BlockchainCommons/lethekit/doc/images/lethekit-1280x640.jpg

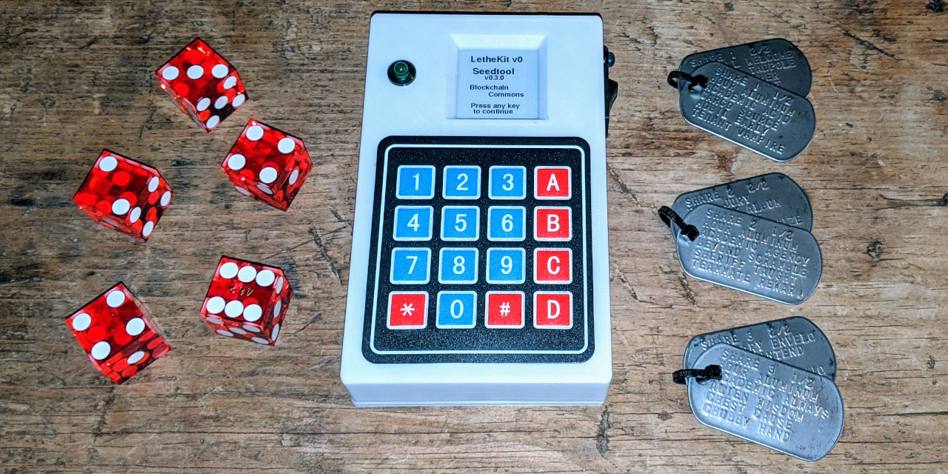
doc/images/lethekit-1280x640.jpg
