BlockchainCommons/lethekit/images/lk-xpub+prv-ex.jpg

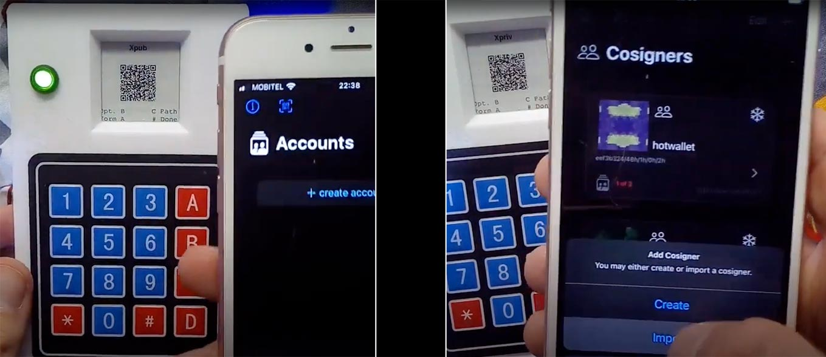
images/lk-xpub+prv-ex.jpg
