BlockchainCommons/lethekit/lethekit.jpg

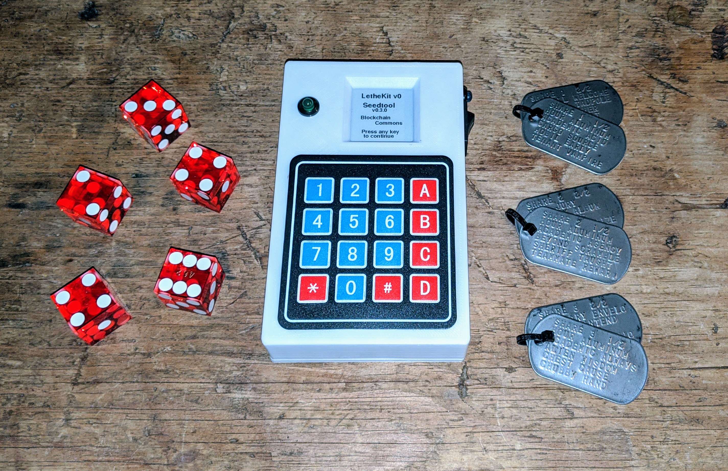
lethekit.jpg
