BlockchainCommons/lethekit/seedtool/doc/images/wallet.png

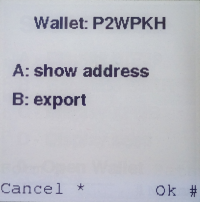
seedtool/doc/images/wallet.png
