BlockchainCommons/lethekit/deps/bc-ur-arduino/src/fountain-encoder.hpp

//
//  fountain-encoder.hpp
//
//  Copyright © 2020 by Blockchain Commons, LLC
//  Licensed under the "BSD-2-Clause Plus Patent License"
//

#ifndef BC_UR_FOUNTAIN_ENCODER_HPP
#define BC_UR_FOUNTAIN_ENCODER_HPP

#include <stddef.h>
#include <vector>
#include <exception>
#include "utils.hpp"
//#include "util.h"
#include "fountain-utils.hpp"

namespace ur_arduino {

// Implements Luby transform code rateless coding
// https://en.wikipedia.org/wiki/Luby_transform_code

class FountainEncoder final {
public:
    class Part {
    public:
        class InvalidHeader: public std::exception { };

        Part(uint32_t seq_num, size_t seq_len, size_t message_len, uint32_t checksum, const ByteVector& data) 
            : seq_num_(seq_num), seq_len_(seq_len), message_len_(message_len), checksum_(checksum), data_(data)
        { }
        Part(const ByteVector& cbor);

        uint32_t seq_num() const { return seq_num_; }
        size_t seq_len() const { return seq_len_; }
        size_t message_len() const { return message_len_; }
        uint32_t checksum() const { return checksum_; }
        const ByteVector& data() const { return data_; }

        ByteVector cbor() const;
        std::string description() const;

    private:
        uint32_t seq_num_;
        size_t seq_len_;
        size_t message_len_;
        uint32_t checksum_;
        ByteVector data_;
    };

    FountainEncoder(const ByteVector& message, size_t max_fragment_len, uint32_t first_seq_num = 0, size_t min_fragment_len = 10);
    
    static size_t find_nominal_fragment_length(size_t message_len, size_t min_fragment_len, size_t max_fragment_len);
    static std::vector<ByteVector> partition_message(ByteVector message, size_t fragment_len);

    uint32_t seq_num() const { return seq_num_; }
    const PartIndexes& last_part_indexes() const { return last_part_indexes_; }
    size_t seq_len() const { return fragments_.size(); }

    // This becomes `true` when the minimum number of parts
    // to relay the complete message have been generated
    bool is_complete() const { return seq_num_ >= seq_len(); }

    /// True if only a single part will be generated.
    bool is_single_part() const { return seq_len() == 1; }

    Part next_part();

private:
    size_t message_len_;
    uint32_t checksum_;
    size_t fragment_len_;
    std::vector<ByteVector> fragments_;
    uint32_t seq_num_;
    PartIndexes last_part_indexes_;

    ByteVector mix(const PartIndexes& indexes) const;
};

}

#endif // BC_UR_FOUNTAIN_ENCODER_HPP
