BlockchainCommons/lethekit/seedtool/seed.h

// Copyright © 2020 Blockchain Commons, LLC

#ifndef SEED_H
#define SEED_H

#include <stdint.h>

#include <bc-bip39.h>
#include "util.h"
#include "bc-bytewords.h"
#include "CborEncoder.h"

#define BIP39_SEED_LEN_512 64

class Seed {
public:
    static size_t const SIZE = 16;

    static Seed * from_rolls(String const & rolls, uint8_t *trng_entropy = NULL, uint8_t trng_entropy_size = 0);

    Seed(uint8_t const * data, size_t len);

    bool operator==(Seed const & other) const {
        return memcmp(data, other.data, SIZE) == 0;
    }

    bool operator!=(Seed const & other) const {
        return memcmp(data, other.data, SIZE) != 0;
    }

    void log() const;

    uint8_t data[SIZE];
};

class BIP39Seq {
public:
    static size_t const WORD_COUNT = 12;

    static BIP39Seq * from_words(uint16_t * words);

    uint8_t mnemonic_seed[BIP39_SEED_LEN_512];

    BIP39Seq();

    BIP39Seq(Seed const * seed);

    ~BIP39Seq();

    void set_word(size_t ndx, uint16_t word);

    // Return the char string for a dictionary index.
    static String get_dict_string(size_t ndx);

    // Return the word for a word list index.
    uint16_t get_word(size_t ndx) const;

    // Return the char string for a list index.
    String get_string(size_t ndx);

    // Returns NULL if restore fails (bad BIP39 checksum).
    Seed * restore_seed() const;

    // fix_bip39_checksum is only intended for when user wants
    // to generate seed from bip39 words
    void fix_bip39_checksum(void) { bip39_append_checksum(ctx); }

    // we need to have full menmonic words saved as string
    // which is needed to calculate mnemonic seed
    String get_mnemonic_as_string();

private:
    void* ctx;
    // menmonic seed is needed for bip32 root key
    // len of the returned bytes is BIP39_SEED_LEN_512
    bool calc_mnemonic_seed();
};

class SSKRShareSeq {
public:
    static size_t const MAX_SHARES = 16;

    // we currently support only 16 byte seed, therefore WORDS_PER_SHARE and BYTES_PER_SHARE are a constant
    static size_t const WORDS_PER_SHARE = 29;
    static size_t const BYTES_PER_SHARE = 21;

    const size_t METADATA_LENGTH_BYTES = 5;

    static SSKRShareSeq * from_seed(Seed const * seed,
                                      uint8_t thresh,
                                      uint8_t nshares,
                                      void(*randgen)(uint8_t *, size_t, void *));

    // Read-only, don't free returned value.
    uint8_t const * get_share(size_t ndx) const;

    // Adds a copy of the argument, returns the share index.
    size_t add_share(uint8_t const * share);

    // Replace a share's value with a copy of the argument.
    void set_share(size_t ndx, uint8_t const * share, size_t len);

    // Returns NULL if restore fails, use last_error for diagnostic.
    Seed * restore_seed() const;

    // Delete the specified share, compact gaps.
    void del_share(size_t ndx);

    // get share from ur message ur:crypto-sskr
    bool get_share_from_ur(String bytewords, size_t sskr_shard_indx);

    // Read only, don't free returned value.
    String get_share_word(int sharendx, int wndx);

    String get_share_strings(size_t ndx) const;

    size_t numshares() const { return nshares; }

    int last_restore_error() { return last_rv; }

    uint8_t *shares[MAX_SHARES]; // shares in bytes format
    String shares_ur[MAX_SHARES]; // shares in ur format   @TODO: getter
    String shares_bytewords[MAX_SHARES]; // shares in bytewords format @TODO: getter
    size_t shares_len; // threshold
    size_t bytes_in_each_share;

private:
    size_t nshares;
    mutable int last_rv;
};


/**
 *  This function is taken from libwally. We cannot import libwally_bip39 because it is clashing with
 *  bc-bip39.h. bc-bip39.h should be deprecated and replaced with libwally_bip39. To recompile libwally
 *  with libwally_bip39 uncomment the lines in blacklist array in scripts/libwally_build.py
 *  See https://github.com/BlockchainCommons/bc-bip39/pull/19
 */
int bip39_mnemonic_to_seed(const char *mnemonic, const char *passphrase,
                            unsigned char *bytes_out, size_t len,
                            size_t *written);

#endif // SEED_H
