BlockchainCommons/lethekit/deps/bc-ur-arduino/src/bc-ur.hpp

//
//  bc-ur.hpp
//
//  Copyright © 2020 by Blockchain Commons, LLC
//  Licensed under the "BSD-2-Clause Plus Patent License"
//

#ifndef BC_UR_HPP
#define BC_UR_HPP

#include "ur_.hpp"
#include "ur-encoder.hpp"
//#include "ur-decoder.hpp"
#include "fountain-encoder.hpp"
//#include "fountain-decoder.hpp"
#include "fountain-utils.hpp"
#include "utils.hpp"
#include "bytewords.hpp"
#include "xoshiro256.hpp"
#include "random-sampler.hpp"

namespace ur_arduino {

//#include "cbor-lite.hpp"

}

#endif // BC_UR_HPP
