BlockchainCommons/lethekit/seedtool/test_bc_ur.ino

#include "test_bc_ur.hpp"


using namespace ur_arduino;
using namespace std;

typedef std::vector<uint8_t> ByteVector;


void test_rng_1(void) {
    auto rng = Xoshiro256("Wolf");
    vector<uint64_t> numbers;
    for(int i = 0; i < 100; i++) {
        numbers.push_back(rng.next() % 100);
    }
    vector<uint64_t> expected_numbers = {42, 81, 85, 8, 82, 84, 76, 73, 70, 88, 2, 74, 40, 48, 77, 54, 88, 7, 5, 88, 37, 25, 82, 13, 69, 59, 30, 39, 11, 82, 19, 99, 45, 87, 30, 15, 32, 22, 89, 44, 92, 77, 29, 78, 4, 92, 44, 68, 92, 69, 1, 42, 89, 50, 37, 84, 63, 34, 32, 3, 17, 62, 40, 98, 82, 89, 24, 43, 85, 39, 15, 3, 99, 29, 20, 42, 27, 10, 85, 66, 50, 35, 69, 70, 70, 74, 30, 13, 72, 54, 11, 5, 70, 55, 91, 52, 10, 43, 43, 52};

    for(int i=0; i < expected_numbers.size(); i++) {
        serial_assert(expected_numbers.at(i) == numbers.at(i));
    }
}

void test_rng_2() {
    auto checksum = bytes_to_int(crc32_bytes(string_to_bytes("Wolf")));
    auto rng = Xoshiro256(checksum);
    vector<uint64_t> numbers;
    for(int i = 0; i < 100; i++) {
        numbers.push_back(rng.next() % 100);
    }
    vector<uint64_t> expected_numbers = {88, 44, 94, 74, 0, 99, 7, 77, 68, 35, 47, 78, 19, 21, 50, 15, 42, 36, 91, 11, 85, 39, 64, 22, 57, 11, 25, 12, 1, 91, 17, 75, 29, 47, 88, 11, 68, 58, 27, 65, 21, 54, 47, 54, 73, 83, 23, 58, 75, 27, 26, 15, 60, 36, 30, 21, 55, 57, 77, 76, 75, 47, 53, 76, 9, 91, 14, 69, 3, 95, 11, 73, 20, 99, 68, 61, 3, 98, 36, 98, 56, 65, 14, 80, 74, 57, 63, 68, 51, 56, 24, 39, 53, 80, 57, 51, 81, 3, 1, 30};
    
    for(int i=0; i < expected_numbers.size(); i++) {
        //serial_assert(expected_numbers.at(i) == numbers.at(i));
        std::cout << (uint32_t)numbers.at(i) << ' ';
    }

    for(int i=0; i < expected_numbers.size(); i++) {
        //serial_assert(expected_numbers.at(i) == numbers.at(i));
        std::cout << (uint32_t)expected_numbers.at(i) << ' ';
    }
}

void test_rng_3() {
    auto rng = Xoshiro256("Wolf");
    vector<uint64_t> numbers;
    for(int i = 0; i < 100; i++) {
        numbers.push_back(rng.next_int(1, 10));
    }

    vector<uint64_t> expected_numbers = {6, 5, 8, 4, 10, 5, 7, 10, 4, 9, 10, 9, 7, 7, 1, 1, 2, 9, 9, 2, 6, 4, 5, 7, 8, 5, 4, 2, 3, 8, 7, 4, 5, 1, 10, 9, 3, 10, 2, 6, 8, 5, 7, 9, 3, 1, 5, 2, 7, 1, 4, 4, 4, 4, 9, 4, 5, 5, 6, 9, 5, 1, 2, 8, 3, 3, 2, 8, 4, 3, 2, 1, 10, 8, 9, 3, 10, 8, 5, 5, 6, 7, 10, 5, 8, 9, 4, 6, 4, 2, 10, 2, 1, 7, 9, 6, 7, 4, 2, 5};
    
    for(int i=0; i < expected_numbers.size(); i++) {
        serial_assert(expected_numbers.at(i) == numbers.at(i));
    }

}

void test_find_fragment_length() {
    serial_assert(FountainEncoder::find_nominal_fragment_length(12345, 1005, 1955) == 1764);
    serial_assert(FountainEncoder::find_nominal_fragment_length(12345, 1005, 30000) == 12345);
}

void test_random_sampler() {
    vector<double> probs = { 1, 2, 4, 8 };
    auto sampler = RandomSampler(probs);
    auto rng = Xoshiro256("Wolf");
    vector<int> samples;
    auto f = [&](){ return rng.next_double(); };
    for(int i = 0; i < 500; i++) {
        //samples.push_back(sampler.next(f));
        samples.push_back(sampler.next(f(), f()));
    }
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
    auto rejoined_message = FountainDecoder::join_fragments(fragments, message.size());
    serial_assert(message == rejoined_message);
}
*/

// Note: this test is quite heavy for MCU (memory problems). Turned off for now.
void test_choose_degree() {

    Serial.println("test_choose_degree");
    auto message = make_message(1024);
    auto fragment_len = FountainEncoder::find_nominal_fragment_length(message.size(), 10, 100);
    auto fragments = FountainEncoder::partition_message(message, fragment_len);
    vector<size_t> _degrees;
    char * nonce_str = NULL;
    string nonce_string;
    for(int nonce = 1; nonce <= 200; nonce++) {
        char * nonce_str = (char *)String(nonce).c_str();
        nonce_string = nonce_str;
        auto part_rng = Xoshiro256("Wolf-" + nonce_string);
        _degrees.push_back(choose_degree(fragments.size(), part_rng));
    }

    //for(int i=0; i < degrees.size(); i++) {
    //    Serial.print(degrees.at(i));
    //}
    //Serial.println("");

    vector<size_t> expected_degrees = {11, 3, 6, 5, 2, 1, 2, 11, 1, 3, 9, 10, 10, 4, 2, 1, 1, 2, 1, 1, 5, 2, 4, 10, 3, 2, 1, 1, 3, 11, 2, 6, 2, 9, 9, 2, 6, 7, 2, 5, 2, 4, 3, 1, 6, 11, 2, 11, 3, 1, 6, 3, 1, 4, 5, 3, 6, 1, 1, 3, 1, 2, 2, 1, 4, 5, 1, 1, 9, 1, 1, 6, 4, 1, 5, 1, 2, 2, 3, 1, 1, 5, 2, 6, 1, 7, 11, 1, 8, 1, 5, 1, 1, 2, 2, 6, 4, 10, 1, 2, 5, 5, 5, 1, 1, 4, 1, 1, 1, 3, 5, 5, 5, 1, 4, 3, 3, 5, 1, 11, 3, 2, 8, 1, 2, 1, 1, 4, 5, 2, 1, 1, 1, 5, 6, 11, 10, 7, 4, 7, 1, 5, 3, 1, 1, 9, 1, 2, 5, 5, 2, 2, 3, 10, 1, 3, 2, 3, 3, 1, 1, 2, 1, 3, 2, 2, 1, 3, 8, 4, 1, 11, 6, 3, 1, 1, 1, 1, 1, 3, 1, 2, 1, 10, 1, 1, 8, 2, 7, 1, 2, 1, 9, 2, 10, 2, 1, 3, 4, 10};
    serial_assert(_degrees == expected_degrees);
}

static void test_choose_fragments() {
    auto message = make_message(1024);
    auto checksum = crc32_int(message);
    auto fragment_len = FountainEncoder::find_nominal_fragment_length(message.size(), 10, 100);
    auto fragments = FountainEncoder::partition_message(message, fragment_len);
    vector<vector<size_t>> fragment_indexes;
    for(uint32_t seq_num = 1; seq_num <= 30; seq_num++) {
        auto indexes_set = choose_fragments(seq_num, fragments.size(), checksum);
        auto indexes = vector<size_t>(indexes_set.begin(), indexes_set.end());
        sort(indexes.begin(), indexes.end());

        fragment_indexes.push_back(indexes);
    }
    vector<vector<size_t>> expected_fragment_indexes = {
        {0},
        {1},
        {2},
        {3},
        {4},
        {5},
        {6},
        {7},
        {8},
        {9},
        {10},
        {9},
        {2, 5, 6, 8, 9, 10},
        {8},
        {1, 5},
        {1},
        {0, 2, 4, 5, 8, 10},
        {5},
        {2},
        {2},
        {0, 1, 3, 4, 5, 7, 9, 10},
        {0, 1, 2, 3, 5, 6, 8, 9, 10},
        {0, 2, 4, 5, 7, 8, 9, 10},
        {3, 5},
        {4},
        {0, 1, 2, 3, 4, 5, 6, 7, 8, 9, 10},
        {0, 1, 3, 4, 5, 6, 7, 9, 10},
        {6},
        {5, 6},
        {7}
    };

    serial_assert(fragment_indexes == expected_fragment_indexes);
}

void test_xor() {
    auto rng = Xoshiro256("Wolf");
    auto data1 = rng.next_data(10);
    serial_assert(data_to_hex(data1) == "916ec65cf77cadf55cd7");
    auto data2 = rng.next_data(10);
    serial_assert(data_to_hex(data2) == "f9cda1a1030026ddd42e");
    auto data3 = data1;
    xor_into(data3, data2);
    serial_assert(data_to_hex(data3) == "68a367fdf47c8b2888f9");
    xor_into(data3, data1);
    serial_assert(data3 == data2);
}

void test_fountain_encoder() {
    auto message = make_message(256);
    auto encoder = FountainEncoder(message, 30);
    StringVector parts;
    for(int i = 0; i < 20; i++) {
        parts.push_back(encoder.next_part().description());
    }
    StringVector expected_parts = {
        "seqNum:1, seqLen:9, messageLen:256, checksum:23570951, data:916ec65cf77cadf55cd7f9cda1a1030026ddd42e905b77adc36e4f2d3c",
        "seqNum:2, seqLen:9, messageLen:256, checksum:23570951, data:cba44f7f04f2de44f42d84c374a0e149136f25b01852545961d55f7f7a",
        "seqNum:3, seqLen:9, messageLen:256, checksum:23570951, data:8cde6d0e2ec43f3b2dcb644a2209e8c9e34af5c4747984a5e873c9cf5f",
        "seqNum:4, seqLen:9, messageLen:256, checksum:23570951, data:965e25ee29039fdf8ca74f1c769fc07eb7ebaec46e0695aea6cbd60b3e",
        "seqNum:5, seqLen:9, messageLen:256, checksum:23570951, data:c4bbff1b9ffe8a9e7240129377b9d3711ed38d412fbb4442256f1e6f59",
        "seqNum:6, seqLen:9, messageLen:256, checksum:23570951, data:5e0fc57fed451fb0a0101fb76b1fb1e1b88cfdfdaa946294a47de8fff1",
        "seqNum:7, seqLen:9, messageLen:256, checksum:23570951, data:73f021c0e6f65b05c0a494e50791270a0050a73ae69b6725505a2ec8a5",
        "seqNum:8, seqLen:9, messageLen:256, checksum:23570951, data:791457c9876dd34aadd192a53aa0dc66b556c0c215c7ceb8248b717c22",
        "seqNum:9, seqLen:9, messageLen:256, checksum:23570951, data:951e65305b56a3706e3e86eb01c803bbf915d80edcd64d4d0000000000",
        "seqNum:10, seqLen:9, messageLen:256, checksum:23570951, data:330f0f33a05eead4f331df229871bee733b50de71afd2e5a79f196de09",
        "seqNum:11, seqLen:9, messageLen:256, checksum:23570951, data:3b205ce5e52d8c24a52cffa34c564fa1af3fdffcd349dc4258ee4ee828",
        "seqNum:12, seqLen:9, messageLen:256, checksum:23570951, data:dd7bf725ea6c16d531b5f03254783803048ca08b87148daacd1cd7a006",
        "seqNum:13, seqLen:9, messageLen:256, checksum:23570951, data:760be7ad1c6187902bbc04f539b9ee5eb8ea6833222edea36031306c01",
        "seqNum:14, seqLen:9, messageLen:256, checksum:23570951, data:5bf4031217d2c3254b088fa7553778b5003632f46e21db129416f65b55",
        "seqNum:15, seqLen:9, messageLen:256, checksum:23570951, data:73f021c0e6f65b05c0a494e50791270a0050a73ae69b6725505a2ec8a5",
        "seqNum:16, seqLen:9, messageLen:256, checksum:23570951, data:b8546ebfe2048541348910267331c643133f828afec9337c318f71b7df",
        "seqNum:17, seqLen:9, messageLen:256, checksum:23570951, data:23dedeea74e3a0fb052befabefa13e2f80e4315c9dceed4c8630612e64",
        "seqNum:18, seqLen:9, messageLen:256, checksum:23570951, data:d01a8daee769ce34b6b35d3ca0005302724abddae405bdb419c0a6b208",
        "seqNum:19, seqLen:9, messageLen:256, checksum:23570951, data:3171c5dc365766eff25ae47c6f10e7de48cfb8474e050e5fe997a6dc24",
        "seqNum:20, seqLen:9, messageLen:256, checksum:23570951, data:e055c2433562184fa71b4be94f262e200f01c6f74c284b0dc6fae6673f"
    };
    serial_assert(parts == expected_parts);
}

static void test_fountain_encoder_cbor() {
    auto message = make_message(256);
    auto encoder = FountainEncoder(message, 30);
    StringVector parts;
    for(int i = 0; i < 20; i++) {
        parts.push_back(data_to_hex(encoder.next_part().cbor()));
    }
    StringVector expected_parts = {
        "8501091901001a0167aa07581d916ec65cf77cadf55cd7f9cda1a1030026ddd42e905b77adc36e4f2d3c",
        "8502091901001a0167aa07581dcba44f7f04f2de44f42d84c374a0e149136f25b01852545961d55f7f7a",
        "8503091901001a0167aa07581d8cde6d0e2ec43f3b2dcb644a2209e8c9e34af5c4747984a5e873c9cf5f",
        "8504091901001a0167aa07581d965e25ee29039fdf8ca74f1c769fc07eb7ebaec46e0695aea6cbd60b3e",
        "8505091901001a0167aa07581dc4bbff1b9ffe8a9e7240129377b9d3711ed38d412fbb4442256f1e6f59",
        "8506091901001a0167aa07581d5e0fc57fed451fb0a0101fb76b1fb1e1b88cfdfdaa946294a47de8fff1",
        "8507091901001a0167aa07581d73f021c0e6f65b05c0a494e50791270a0050a73ae69b6725505a2ec8a5",
        "8508091901001a0167aa07581d791457c9876dd34aadd192a53aa0dc66b556c0c215c7ceb8248b717c22",
        "8509091901001a0167aa07581d951e65305b56a3706e3e86eb01c803bbf915d80edcd64d4d0000000000",
        "850a091901001a0167aa07581d330f0f33a05eead4f331df229871bee733b50de71afd2e5a79f196de09",
        "850b091901001a0167aa07581d3b205ce5e52d8c24a52cffa34c564fa1af3fdffcd349dc4258ee4ee828",
        "850c091901001a0167aa07581ddd7bf725ea6c16d531b5f03254783803048ca08b87148daacd1cd7a006",
        "850d091901001a0167aa07581d760be7ad1c6187902bbc04f539b9ee5eb8ea6833222edea36031306c01",
        "850e091901001a0167aa07581d5bf4031217d2c3254b088fa7553778b5003632f46e21db129416f65b55",
        "850f091901001a0167aa07581d73f021c0e6f65b05c0a494e50791270a0050a73ae69b6725505a2ec8a5",
        "8510091901001a0167aa07581db8546ebfe2048541348910267331c643133f828afec9337c318f71b7df",
        "8511091901001a0167aa07581d23dedeea74e3a0fb052befabefa13e2f80e4315c9dceed4c8630612e64",
        "8512091901001a0167aa07581dd01a8daee769ce34b6b35d3ca0005302724abddae405bdb419c0a6b208",
        "8513091901001a0167aa07581d3171c5dc365766eff25ae47c6f10e7de48cfb8474e050e5fe997a6dc24",
        "8514091901001a0167aa07581de055c2433562184fa71b4be94f262e200f01c6f74c284b0dc6fae6673f"
    };
    serial_assert(parts == expected_parts);
}

void test_fountain_encoder_is_complete() {
    auto message = make_message(256);
    auto encoder = FountainEncoder(message, 30);
    size_t generated_parts_count = 0;
    while(!encoder.is_complete()) {
        encoder.next_part();
        generated_parts_count += 1;
    }
    serial_assert(encoder.seq_len() == generated_parts_count);
}

void test_fountain_cbor() {

    CborDynamicOutput output;
    CborWriter writer(output);

    writer.writeArray(5);
    writer.writeInt(12);
    writer.writeInt(8);
    writer.writeInt(100);
    writer.writeInt(0x12345678);
    uint8_t arr[]  ={1, 5, 3, 3 ,5};
    writer.writeBytes(arr, sizeof(arr));
    ByteVector vec(output.getData(), output.getData() + output.getSize());

    //auto part = FountainEncoder::Part(12, 8, 100, 0x12345678, {1, 5, 3, 3 ,5});
    auto part = FountainEncoder::Part(vec);
    auto cbor = part.cbor();
    auto part2 = FountainEncoder::Part(cbor);
    auto cbor2 = part2.cbor();

    serial_assert(cbor == cbor2);
}

static void test_ur_encoder() {
    auto ur = make_message_ur(256);
    auto encoder = UREncoder(ur, 30);
    StringVector parts;
    for(int i = 0; i < 20; i++) {
        parts.push_back(encoder.next_part());
    }
    StringVector expected_parts = {
        "ur:bytes/1-9/lpadascfadaxcywenbpljkhdcahkadaemejtswhhylkepmykhhtsytsnoyoyaxaedsuttydmmhhpktpmsrjtdkgslpgh",
        "ur:bytes/2-9/lpaoascfadaxcywenbpljkhdcagwdpfnsboxgwlbaawzuefywkdplrsrjynbvygabwjldapfcsgmghhkhstlrdcxaefz",
        "ur:bytes/3-9/lpaxascfadaxcywenbpljkhdcahelbknlkuejnbadmssfhfrdpsbiegecpasvssovlgeykssjykklronvsjksopdzmol",
        "ur:bytes/4-9/lpaaascfadaxcywenbpljkhdcasotkhemthydawydtaxneurlkosgwcekonertkbrlwmplssjtammdplolsbrdzcrtas",
        "ur:bytes/5-9/lpahascfadaxcywenbpljkhdcatbbdfmssrkzmcwnezelennjpfzbgmuktrhtejscktelgfpdlrkfyfwdajldejokbwf",
        "ur:bytes/6-9/lpamascfadaxcywenbpljkhdcackjlhkhybssklbwefectpfnbbectrljectpavyrolkzczcpkmwidmwoxkilghdsowp",
        "ur:bytes/7-9/lpatascfadaxcywenbpljkhdcavszmwnjkwtclrtvaynhpahrtoxmwvwatmedibkaegdosftvandiodagdhthtrlnnhy",
        "ur:bytes/8-9/lpayascfadaxcywenbpljkhdcadmsponkkbbhgsoltjntegepmttmoonftnbuoiyrehfrtsabzsttorodklubbuyaetk",
        "ur:bytes/9-9/lpasascfadaxcywenbpljkhdcajskecpmdckihdyhphfotjojtfmlnwmadspaxrkytbztpbauotbgtgtaeaevtgavtny",
        "ur:bytes/10-9/lpbkascfadaxcywenbpljkhdcahkadaemejtswhhylkepmykhhtsytsnoyoyaxaedsuttydmmhhpktpmsrjtwdkiplzs",
        "ur:bytes/11-9/lpbdascfadaxcywenbpljkhdcahelbknlkuejnbadmssfhfrdpsbiegecpasvssovlgeykssjykklronvsjkvetiiapk",
        "ur:bytes/12-9/lpbnascfadaxcywenbpljkhdcarllaluzmdmgstospeyiefmwejlwtpedamktksrvlcygmzemovovllarodtmtbnptrs",
        "ur:bytes/13-9/lpbtascfadaxcywenbpljkhdcamtkgtpknghchchyketwsvwgwfdhpgmgtylctotzopdrpayoschcmhplffziachrfgd",
        "ur:bytes/14-9/lpbaascfadaxcywenbpljkhdcapazewnvonnvdnsbyleynwtnsjkjndeoldydkbkdslgjkbbkortbelomueekgvstegt",
        "ur:bytes/15-9/lpbsascfadaxcywenbpljkhdcaynmhpddpzmversbdqdfyrehnqzlugmjzmnmtwmrouohtstgsbsahpawkditkckynwt",
        "ur:bytes/16-9/lpbeascfadaxcywenbpljkhdcawygekobamwtlihsnpalnsghenskkiynthdzotsimtojetprsttmukirlrsbtamjtpd",
        "ur:bytes/17-9/lpbyascfadaxcywenbpljkhdcamklgftaxykpewyrtqzhydntpnytyisincxmhtbceaykolduortotiaiaiafhiaoyce",
        "ur:bytes/18-9/lpbgascfadaxcywenbpljkhdcahkadaemejtswhhylkepmykhhtsytsnoyoyaxaedsuttydmmhhpktpmsrjtntwkbkwy",
        "ur:bytes/19-9/lpbwascfadaxcywenbpljkhdcadekicpaajootjzpsdrbalpeywllbdsnbinaerkurspbncxgslgftvtsrjtksplcpeo",
        "ur:bytes/20-9/lpbbascfadaxcywenbpljkhdcayapmrleeleaxpasfrtrdkncffwjyjzgyetdmlewtkpktgllepfrltataztksmhkbot"
    };
    
    serial_assert(parts == expected_parts);
}

bool test_bc_ur(void)
{
  test_rng_1();
  test_rng_2();
  test_rng_3();
  test_find_fragment_length();
  test_random_sampler();
  test_shuffle();
  //test_choose_degree(); // @TODO
  test_choose_fragments();
  test_xor();
  test_fountain_encoder();
  test_fountain_encoder_cbor();
  test_fountain_encoder_is_complete();
  test_fountain_cbor();
  test_ur_encoder();

  return true;
}
