BlockchainCommons/lethekit/deps/bc-ur-arduino/src/utils.cpp

//
//  utils.cpp
//
//  Copyright © 2020 by Blockchain Commons, LLC
//  Licensed under the "BSD-2-Clause Plus Patent License"
//

#include "utils.hpp"

extern "C" {

#include "sha2.h"
#include "crc32.h"

}

#include <vector>
#include <sstream>
#include <algorithm>
#include <cctype>
#include <Arduino.h>

using namespace std;

#define htonl(x) __builtin_bswap32((uint32_t) (x))

static uint32_t _crc32(const uint8_t* bytes, size_t len) {
    static uint32_t* table = NULL;

    if(table == NULL) {
        table = (uint32_t *)malloc(256 * sizeof(uint32_t));
        for(int i = 0; i < 256; i++) {
            uint32_t c = i;
            for(int j = 0; j < 8; j++) {
                c = (c % 2 == 0) ? (c >> 1) : (0xEDB88320 ^ (c >> 1));
            }
            table[i] = c;
        }
    }

    uint32_t crc = ~0;
    for(int i = 0; i < len; i++) {
        uint32_t byte = bytes[i];
        crc = (crc >> 8) ^ table[(crc ^ byte) & 0xFF];
    }
    return ~crc;
}

static uint32_t _crc32n(const uint8_t* bytes, size_t len) {
    return htonl(crc32(bytes, len));
}

namespace ur_arduino {

ByteVector sha256(const ByteVector &buf) {
    uint8_t digest[SHA256_DIGEST_LENGTH];
    sha256_Raw(&buf[0], buf.size(), digest);
    return ByteVector(digest, digest + SHA256_DIGEST_LENGTH);
}

ByteVector crc32_bytes(const ByteVector &buf) {
    uint32_t checksum = _crc32n(&buf[0], buf.size());
    auto cbegin = (uint8_t*)&checksum;
    auto cend = cbegin + sizeof(uint32_t);
    return ByteVector(cbegin, cend);
}

uint32_t crc32_int(const ByteVector &buf) {
    return _crc32(&buf[0], buf.size());
}

ByteVector string_to_bytes(const string& s) {
    return ByteVector(s.begin(), s.end());
}

string data_to_hex(const ByteVector& in) {
    auto hex = "0123456789abcdef";
    string result;
    for(auto c: in) {
        result.append(1, hex[(c >> 4) & 0xF]);
        result.append(1, hex[c & 0xF]);
    }
    return result;
}

string data_to_hex(uint32_t n) {
    return data_to_hex(int_to_bytes(n));
}

ByteVector int_to_bytes(uint32_t n) {
    ByteVector b;
    b.reserve(4);
    b.push_back((n >> 24 & 0xff));
    b.push_back((n >> 16) & 0xff);
    b.push_back((n >> 8) & 0xff);
    b.push_back(n & 0xff);
    return b;
}

uint32_t bytes_to_int(const ByteVector& in) {
    assert(in.size() >= 4);
    uint32_t result = 0;
    result |= in[0] << 24;
    result |= in[1] << 16;
    result |= in[2] << 8;
    result |= in[3];
    return result;
}

string join(const StringVector &strings, const string &separator) {
    ostringstream result;
    bool first = true;
    for(auto s: strings) {
        if(!first) {
            result << separator;
        }
        result << s;
        first = false;
    }
    return result.str();
}

StringVector split(const string& s, char separator) {
	StringVector result;
	string buf;

	for(auto c: s) {
		if(c != separator) {
            buf += c;
        } else if(c == separator && buf.length() > 0) {
            result.push_back(buf);
            buf = "";
        }
	}

	if(buf != "") {
        result.push_back(buf);
    }

	return result;
}

StringVector partition(const string& s, size_t size) {
    StringVector result;
    auto remaining = s;
    while(remaining.length() > 0) {
        result.push_back(take_first(remaining, size));
        remaining = drop_first(remaining, size);
    }
    return result;
}

string take_first(const string &s, size_t count) {
    auto first = s.begin();
    auto c = min(s.size(), count);
    auto last = first + c;
    return string(first, last);
}

string drop_first(const string& s, size_t count) {
    if(count >= s.length()) { return ""; }
    return string(s.begin() + count, s.end());
}

void xor_into(ByteVector& target, const ByteVector& source) {
    auto count = target.size();
    assert(count == source.size());
    for(int i = 0; i < count; i++) {
        target[i] ^= source[i];
    }
}

ByteVector xor_with(const ByteVector& a, const ByteVector& b) {
    auto target = a;
    xor_into(target, b);
    return target;
}

bool is_ur_type(char c) {
    if('a' <= c && c <= 'z') return true;
    if('0' <= c && c <= '9') return true;
    if(c == '-') return true;
    return false;
}

bool is_ur_type(const string& s) {
    for(char c: s) {
        if(!is_ur_type(c)) { return false; }
    }
    return true;
}

string to_lowercase(const string& s) {
    string result;
    transform(s.begin(), s.end(), back_inserter(result), [](char c){ return tolower(c); });
    return result;
}

bool has_prefix(const string& s, const string& prefix) {
    return s.rfind(prefix, 0) == 0;
}

string to_string(int32_t val) {
    const char *tmp = String(val).c_str();
    return tmp;
}

}
