BlockchainCommons/lethekit/deps/bc-ur-arduino/src/fountain-utils.hpp

//
//  fountain-utils.hpp
//
//  Copyright © 2020 by Blockchain Commons, LLC
//  Licensed under the "BSD-2-Clause Plus Patent License"
//

#ifndef BC_UR_FOUNTAIN_UTILS_HPP
#define BC_UR_FOUNTAIN_UTILS_HPP

#include <ArduinoSTL.h>
#include <functional>
#include <vector>
#include <set>
#include <algorithm>
#include <iterator>
#include <stdint.h>
#include "xoshiro256.hpp"

namespace ur_arduino {

typedef std::set<size_t> PartIndexes;

// Fisher-Yates shuffle
template<typename T>
std::vector<T> shuffled(const std::vector<T>& items, Xoshiro256& rng) {
    auto remaining = items;
    std::vector<T> result;
    while(!remaining.empty()) {
        auto index = rng.next_int(0, remaining.size() - 1);
        auto item = remaining[index];
        remaining.erase(remaining.begin() + index);
        result.push_back(item);
    }
    return result;
}

// Return `true` if `a` is a strict subset of `b`.
template<typename T>
bool is_strict_subset(const std::set<T>& a, const std::set<T>& b) {
    if(a == b) { return false; }
    return std::includes(b.begin(), b.end(), a.begin(), a.end());
}

template<typename T>
std::set<T> set_difference(const std::set<T>& a, const std::set<T>& b) {
    std::set<T> result;
    std::set_difference(a.begin(), a.end(), b.begin(), b.end(), std::inserter(result, result.begin()));
    return result;
}

template<typename T>
bool contains(const std::set<T>& s, const T& v) {
    return s.find(v) != s.end();
}

size_t choose_degree(size_t seq_len, Xoshiro256& rng);
std::set<size_t> choose_fragments(uint32_t seq_num, size_t seq_len, uint32_t checksum);

}

#endif // BC_UR_FOUNTAIN_UTILS_HPP
